brubru6707/div-hacks-26/captures/trig_080952.jpg

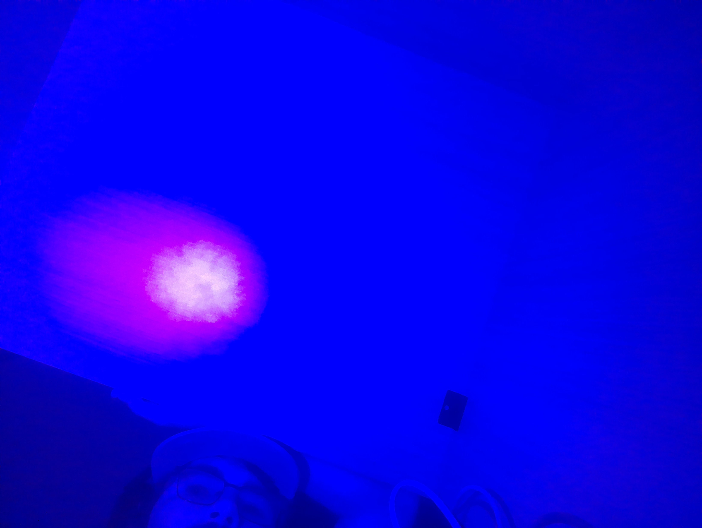
captures/trig_080952.jpg
