brubru6707/div-hacks-26/captures/trig_081049.jpg

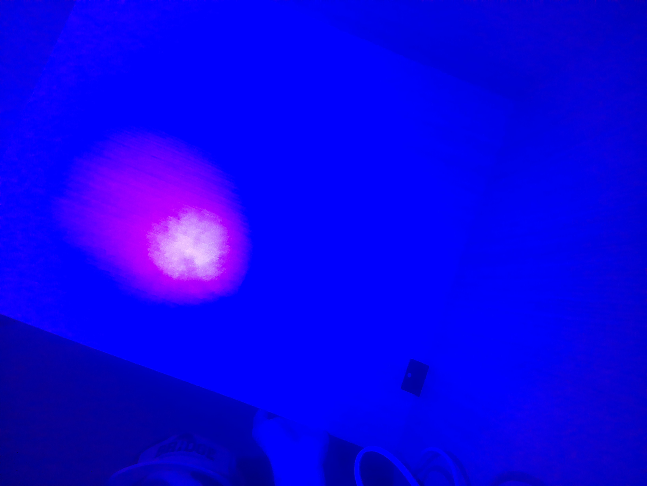
captures/trig_081049.jpg
