brubru6707/div-hacks-26/captures/trig_081102.jpg

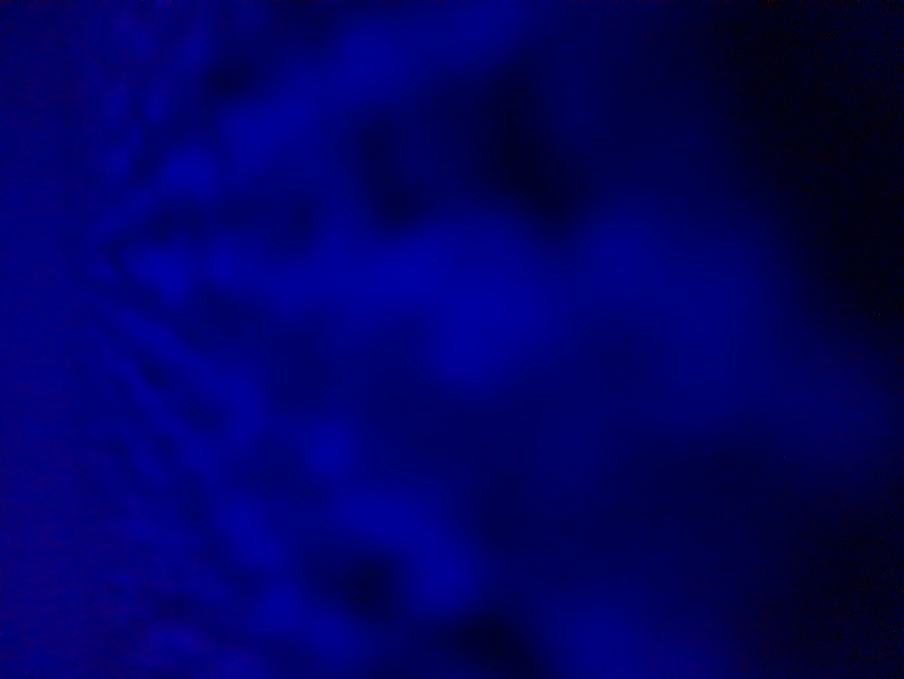
captures/trig_081102.jpg
