brubru6707/div-hacks-26/captures/trig_081107.jpg

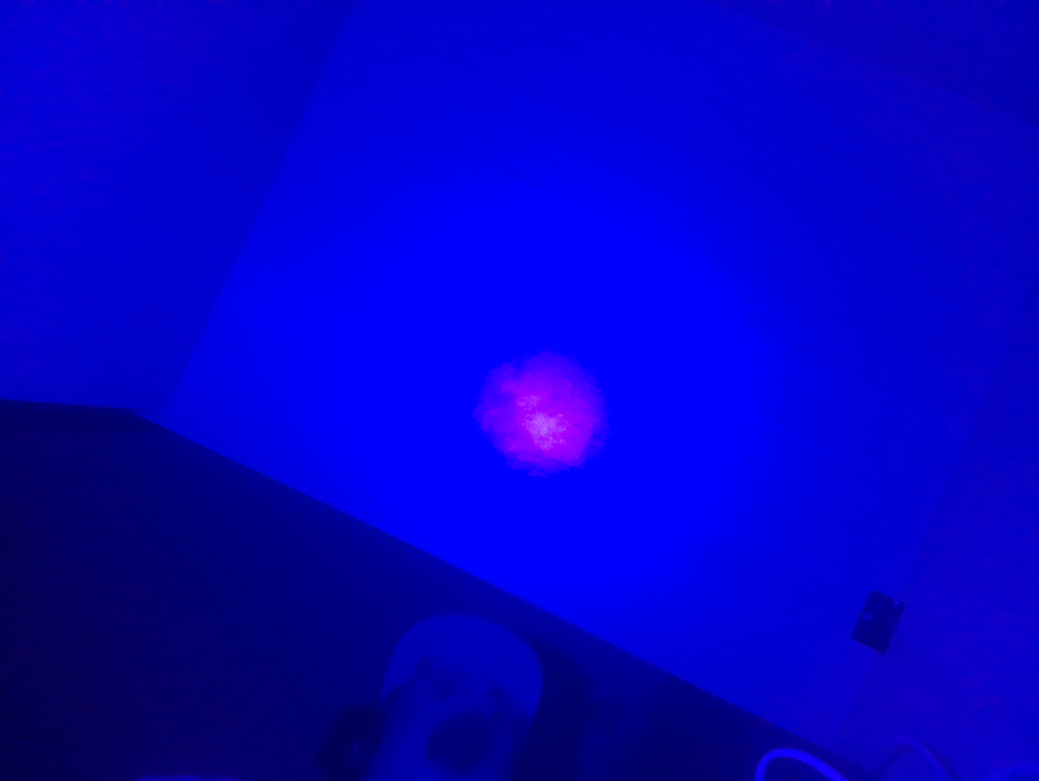
captures/trig_081107.jpg
