brubru6707/div-hacks-26/captures/trig_081144.jpg

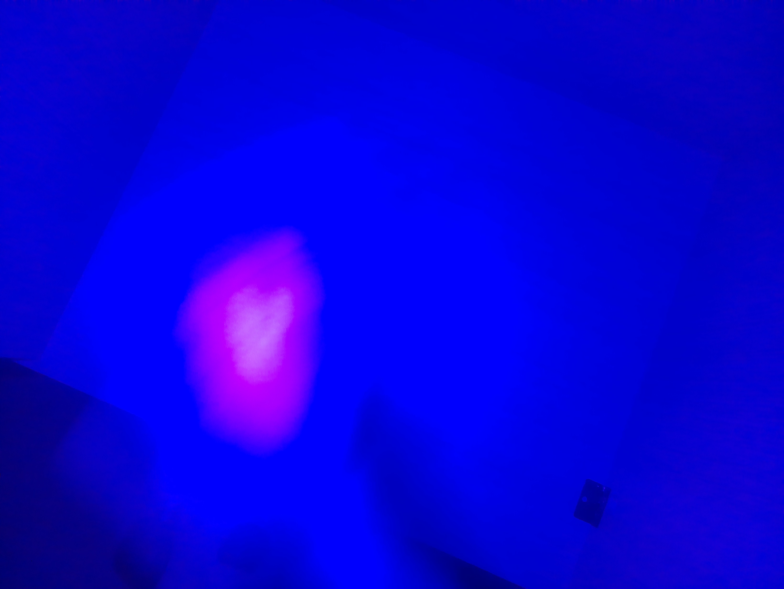
captures/trig_081144.jpg
