brubru6707/div-hacks-26/enclosure/v2/preview/v2_ir_fit_sections.png

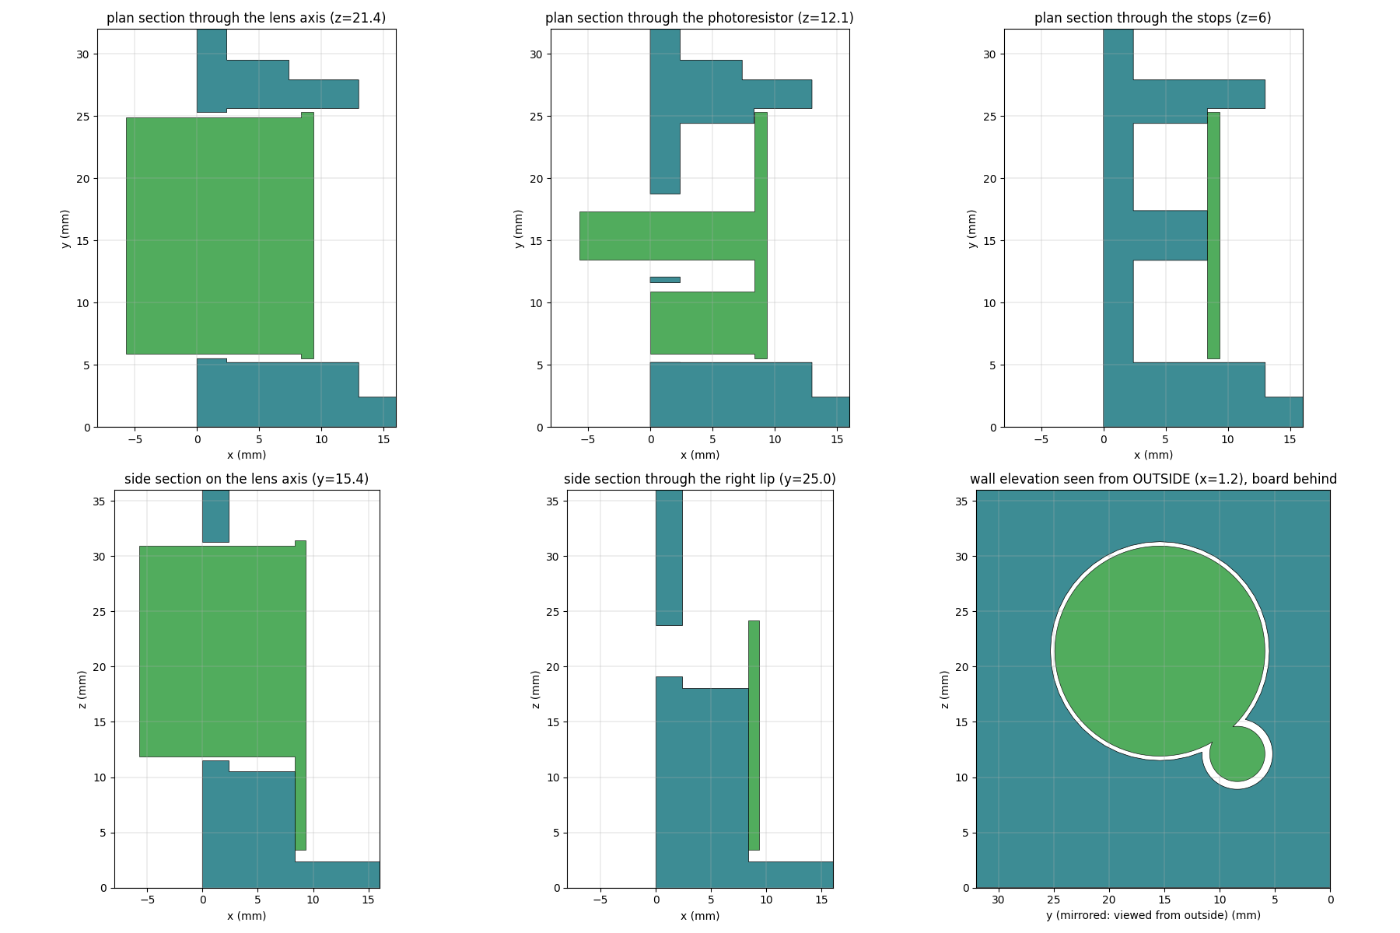
enclosure/v2/preview/v2_ir_fit_sections.png
