brubru6707/div-hacks-26/captures/cam_test.jpg

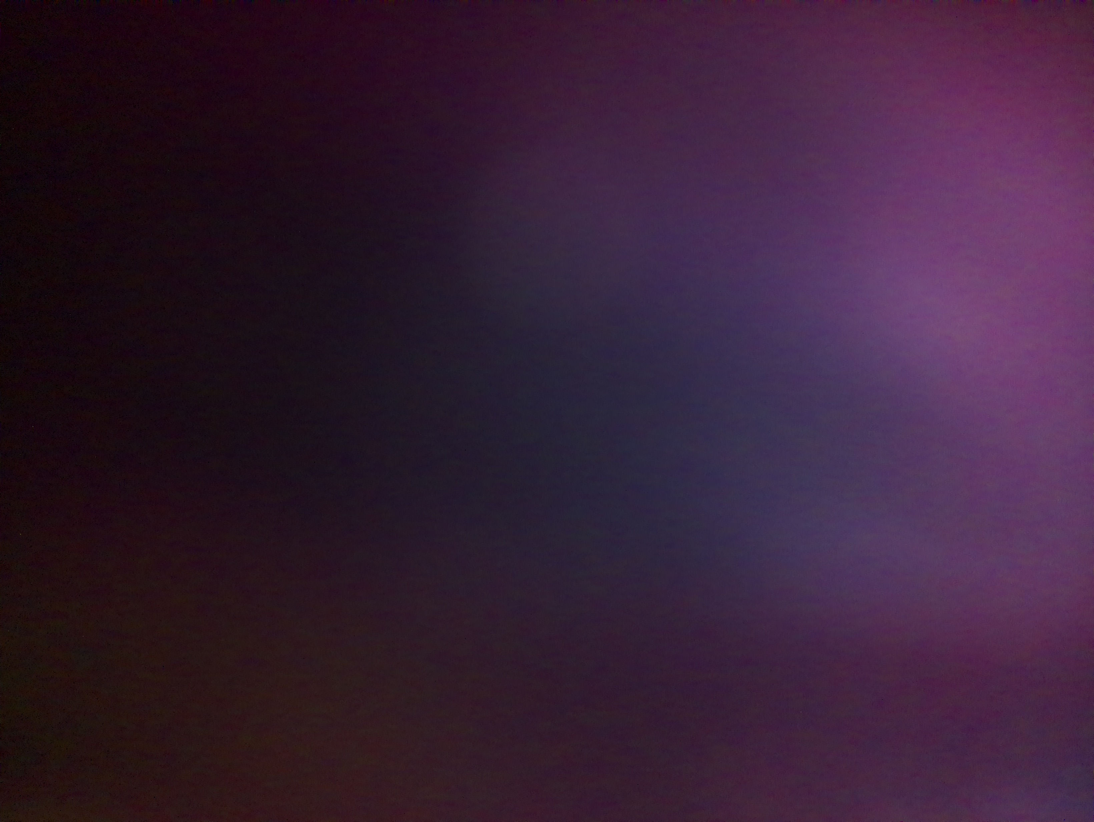
captures/cam_test.jpg
